RafaelEstevamReis/MonitoramentoRios/Montagem/Acessorios/SuporteLoRa.FCStd

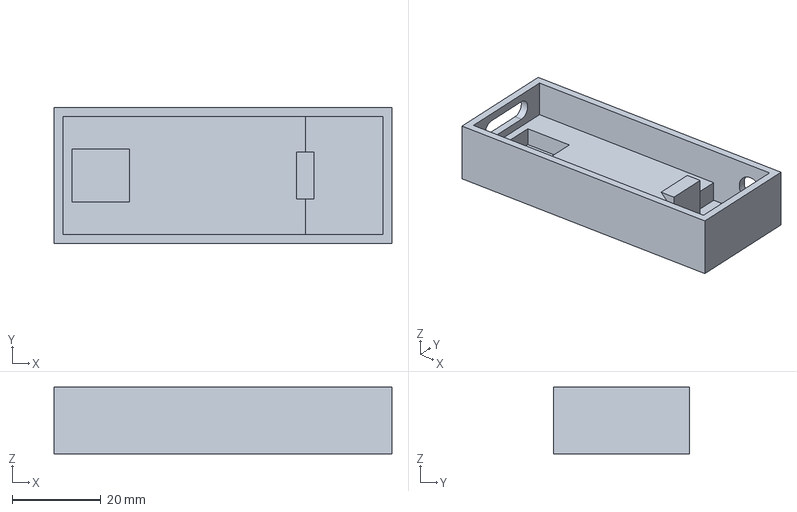
[picture p15: CAD file, 2025-04-11]
Montagem/Acessorios/SuporteLoRa.FCStd
76.0 x 30.5 x 15.0 mm
