RafaelEstevamReis/MonitoramentoRios/Montagem/Acessorios/SuporteLoRa_18650.FCStd

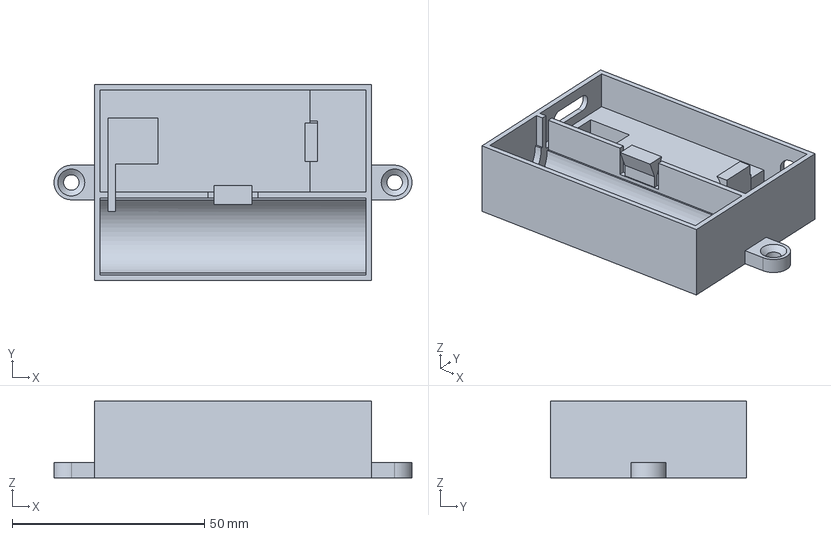
[picture p16: CAD file, 2025-04-11]
Montagem/Acessorios/SuporteLoRa_18650.FCStd
93.0 x 51.0 x 20.0 mm
