RafaelEstevamReis/MonitoramentoRios/Montagem/Acessorios/SuporteLoRa_18650_v2.FCStd

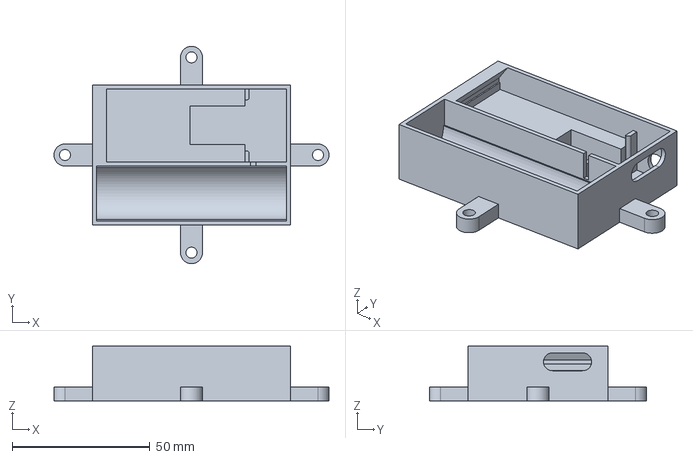
[picture p17: CAD file, 2025-04-11]
Montagem/Acessorios/SuporteLoRa_18650_v2.FCStd
100.0 x 79.0 x 20.0 mm
