RafaelEstevamReis/MonitoramentoRios/Montagem/Acessorios/SuporteCaixa_190x150x90_Tubo.FCStd

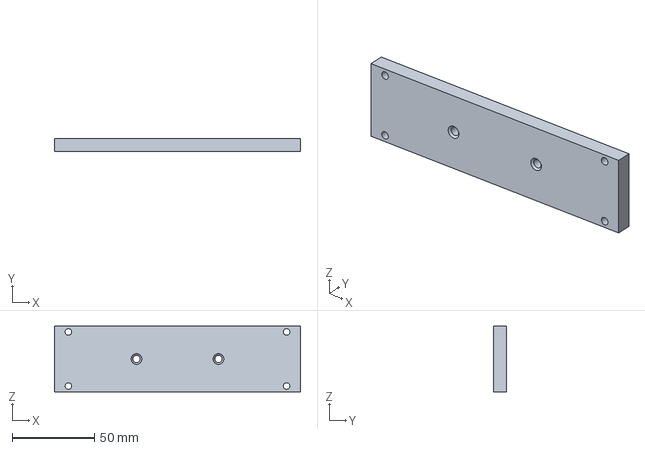
[picture p18: CAD file, 2025-03-26]
Montagem/Acessorios/SuporteCaixa_190x150x90_Tubo.FCStd
150.0 x 8.00 x 40.0 mm
