RafaelEstevamReis/MonitoramentoRios/Montagem/Acessorios/SuporteBateria18650.FCStd

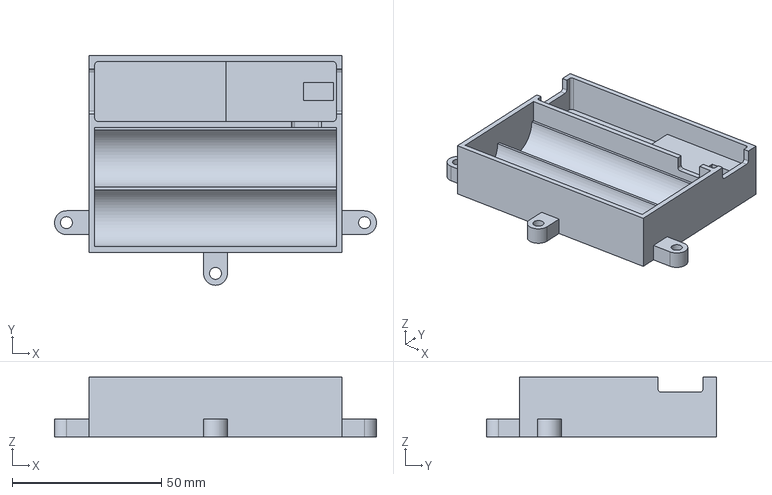
[picture p19: CAD file, 2025-02-10]
Montagem/Acessorios/SuporteBateria18650.FCStd
108.0 x 77.0 x 20.0 mm
